gurues/Clock_Messenger---GITHUB/Instrucciones/Conexiones/Buzzer_Conexion.JPG

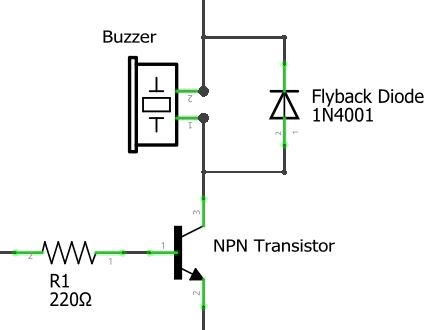
Instrucciones/Conexiones/Buzzer_Conexion.JPG
